xioTechnologies/Calibration-Cube/Sensor Brackets/x-BIMU Bracket.jpg

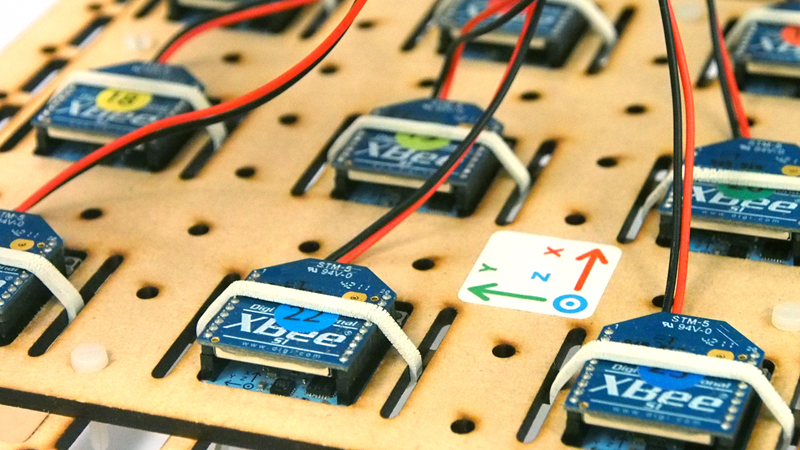
Sensor Brackets/x-BIMU Bracket.jpg
